ximtech/pure-sinus/solr-mobile-power-manager/altium/tl494_pwm_controller/assets/TL494-DIP.jpg

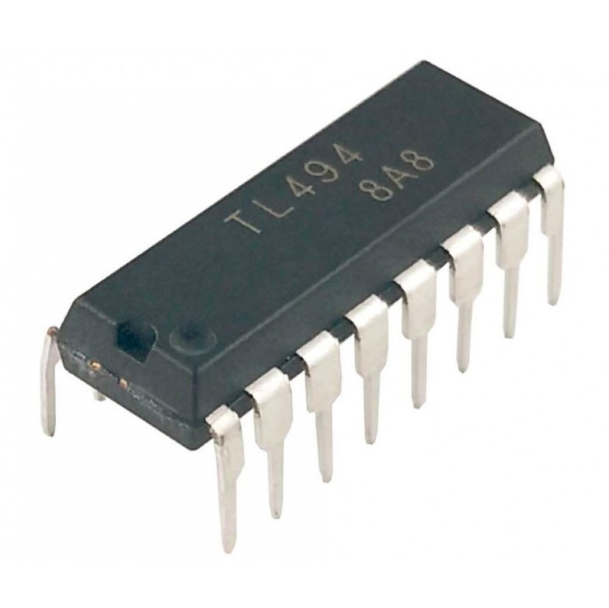
solr-mobile-power-manager/altium/tl494_pwm_controller/assets/TL494-DIP.jpg
