ximtech/pure-sinus/solr-mobile-power-manager/documents/a933c7fd8d9a2fc7b378e1759b0f03b0.png

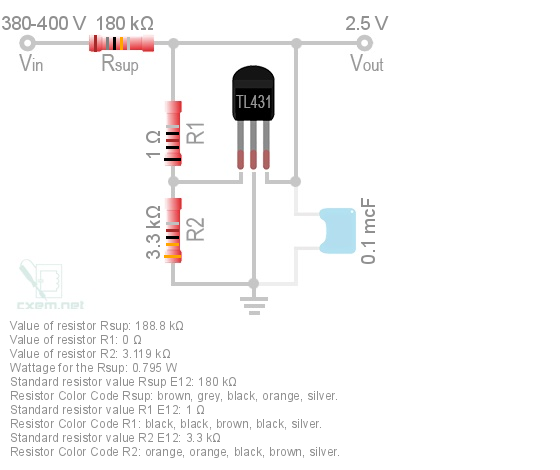
solr-mobile-power-manager/documents/a933c7fd8d9a2fc7b378e1759b0f03b0.png
